carrotIndustries/sd-card-reader-ex/hw/sd-card-reader-flex/PXL_20240421_002655895.jpg

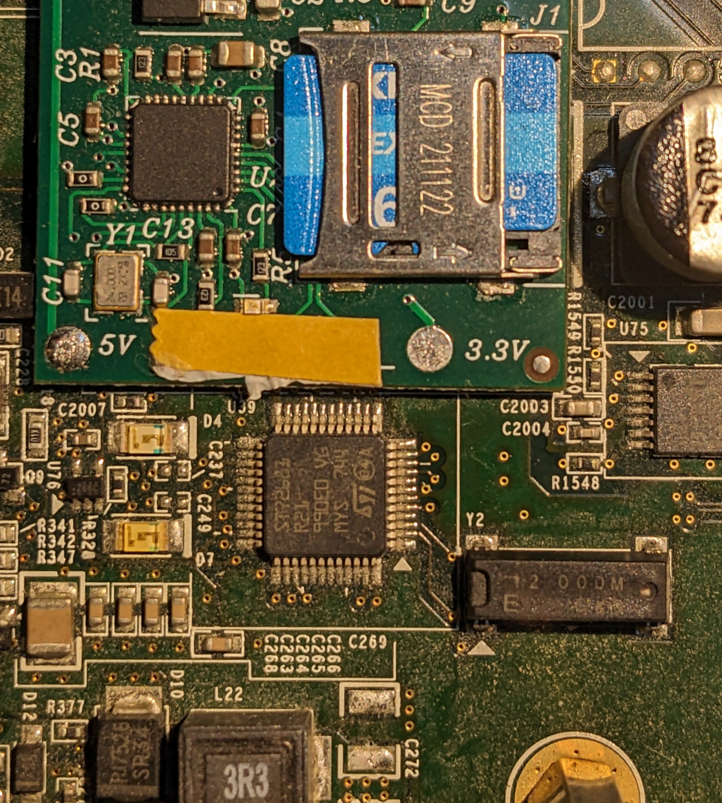
hw/sd-card-reader-flex/PXL_20240421_002655895.jpg
